squaretaper/lisbon-av-install/diagrams/kicad/esp32-led-controller-v6-kicad-bench-schematic.pdf

1 | 2 | 3 | 4 | 5 | 6 | 7 | 8
1 | 2 | 3 | 4 | 5 | 6 | 7 | 8

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
Size: A3 | Rev: v6-kicad-1 | F Date: 2026-05-20
KiCad E.D.A. 10.0.3 | Id: 1/1

# Title: ESP32 LED Controller v6 — KiCad Bench Schematic

## File: esp32-led-controller-v6.kicad_sch

## Sheet: /

## Lisbon AV installation

## ESP32 USB-powered only; common GND; AHCT125 DIP-14 top-view shown for bench wiring

1 2 C3

10µF

1

1

2

2 | J3

12V IN

1 | 2 F1

7.5A blade / off-board inline

1 | 2 R1

470Ω

1 | 2 R3

220Ω

1 | 2 R2

470Ω

A 1 | K

2 LED1

red status

1 | 2 R4

1kΩ +

+

1 -

2 C1

1000µF | / 25V
A 1 | K

2 D1

1N5822? REVIEW CURRENT

A 1 | K

2 LED2

green power-good

notch up / pin 1 upper-left DIP-14 TOP VIEW SN74AHCT125N

/OE1 1

1A 2

1Y 3 | /OE2 4

2A 5

2Y 6 | GND 7
3Y | 8
3A | 9 /OE3 | 10
4Y | | 11
4A | 12 /OE4 | 13
VCC | 14 U1

SN74AHCT125N / 74AHCT125 DIP-14

V+

1 | GND
2 | DATA 3 | J1

LED OUT 1

V+

1 | GND
2 | DATA 3 | J2

LED OUT 2

1 2 C2

0.1µF

VIN/5V = USB tap USB-C powered only ESP32 DevKit V1

GPIO25 | G25 GPIO26 | G26 GPIO27 | G27 GND | GND
VIN/5V | VIN U2
ESP32 DevKit V1 / USB only | U1_2Y U1_1Y GND +12V_IN

GND

GND | +12V_PROTECTED GND +5V_LOGIC

GND

GND +12V_PROTECTED

ESP32_GPIO27

ESP32_GPIO26

J1_DATA U1_1Y | GND
GND | +12V_PROTECTED +5V_LOGIC +5V_LOGIC

GND

# GND +12V_PROTECTED

ESP32_GPIO25 | +12V_PROTECTED +5V_LOGIC | U1_2Y | GND GND

GND

ESP32_GPIO26 | +5V_LOGIC

ESP32_GPIO27

J2_DATA

J1_DATA

# J2_DATA GND

# +5V_LOGIC +12V_IN

### ESP32_GPIO25 12 V POWER INPUT / PROTECTION

U1 unused channels: /OE3 pin10 and /OE4 pin13 → +5V_LOGIC; 3A pin9 and 4A pin12 → GND; 3Y pin8 and 4Y pin11 NC. 5 V LOGIC / STATUS

D1 current note: 1N5822 is not a free pass for multi-amp LED current. For full-current install, replace with rated protection or bypass if polarity is controlled. Bench checks before power: +12V_PROTECTED ↔ +5V_LOGIC = open/megaohms; all GND points ≈0Ω; U1 pin14 gets +5V only from ESP32 USB/VIN; never backfeed ESP32 VIN from 12 V supply.

Rails: +12V_PROTECTED powers LED V+ only. +5V_LOGIC is USB-derived from ESP32 VIN/5V only. Grounds are common. ESP32 LED Controller v6 — KiCad bench schematic

R1

470Ω

1 | 2 R2

470Ω

1 | 2
