squaretaper/lisbon-av-install/diagrams/esp32-led-controller-v6-breadboard.png

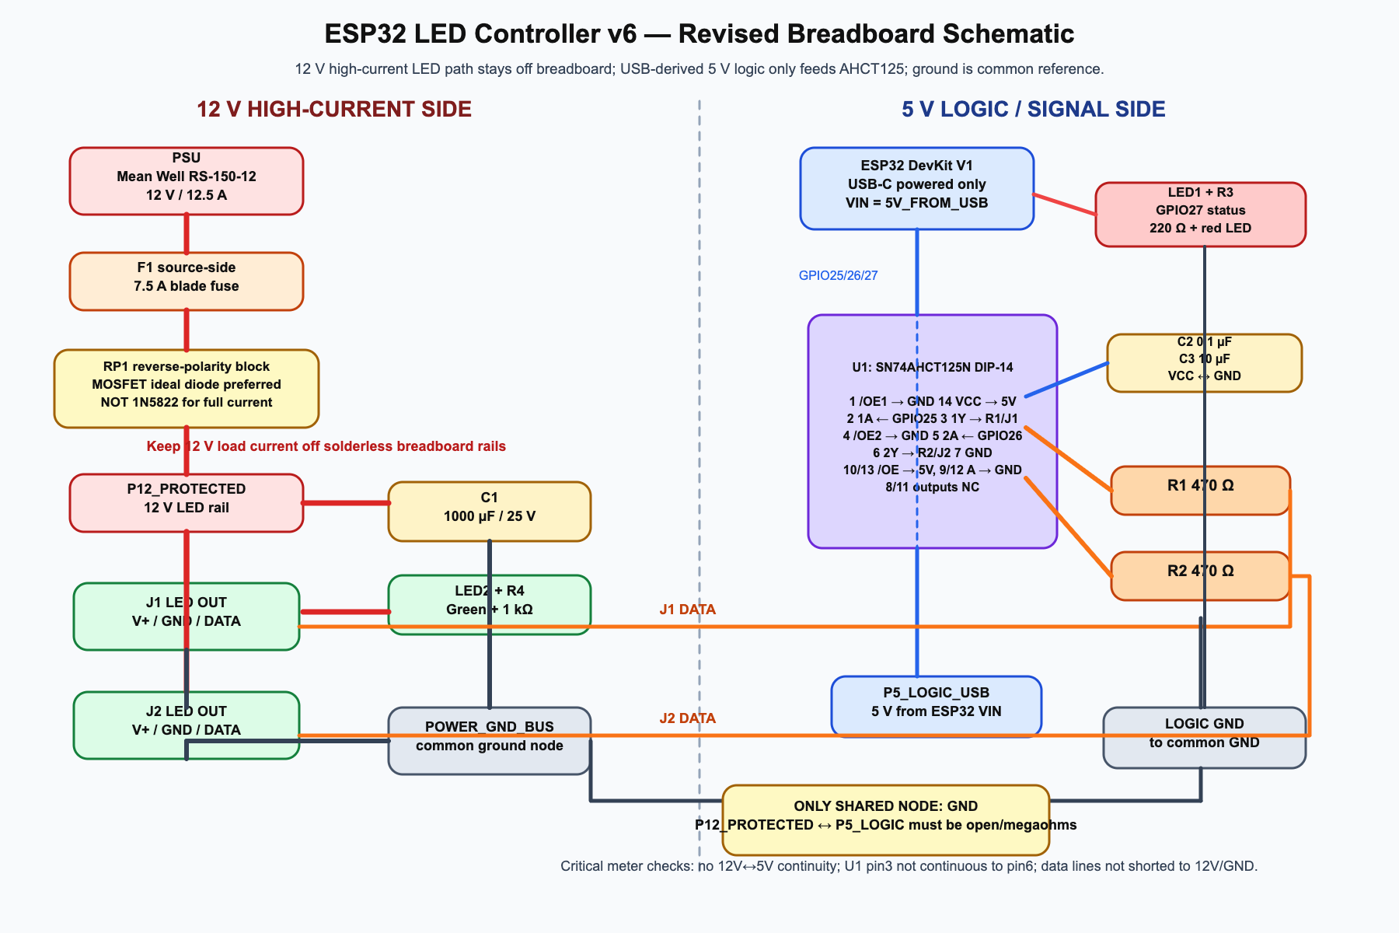
diagrams/esp32-led-controller-v6-breadboard.png
