squaretaper/lisbon-av-install/docs/esp32-breadboard/perfboard-5x7-proposed-layout.png

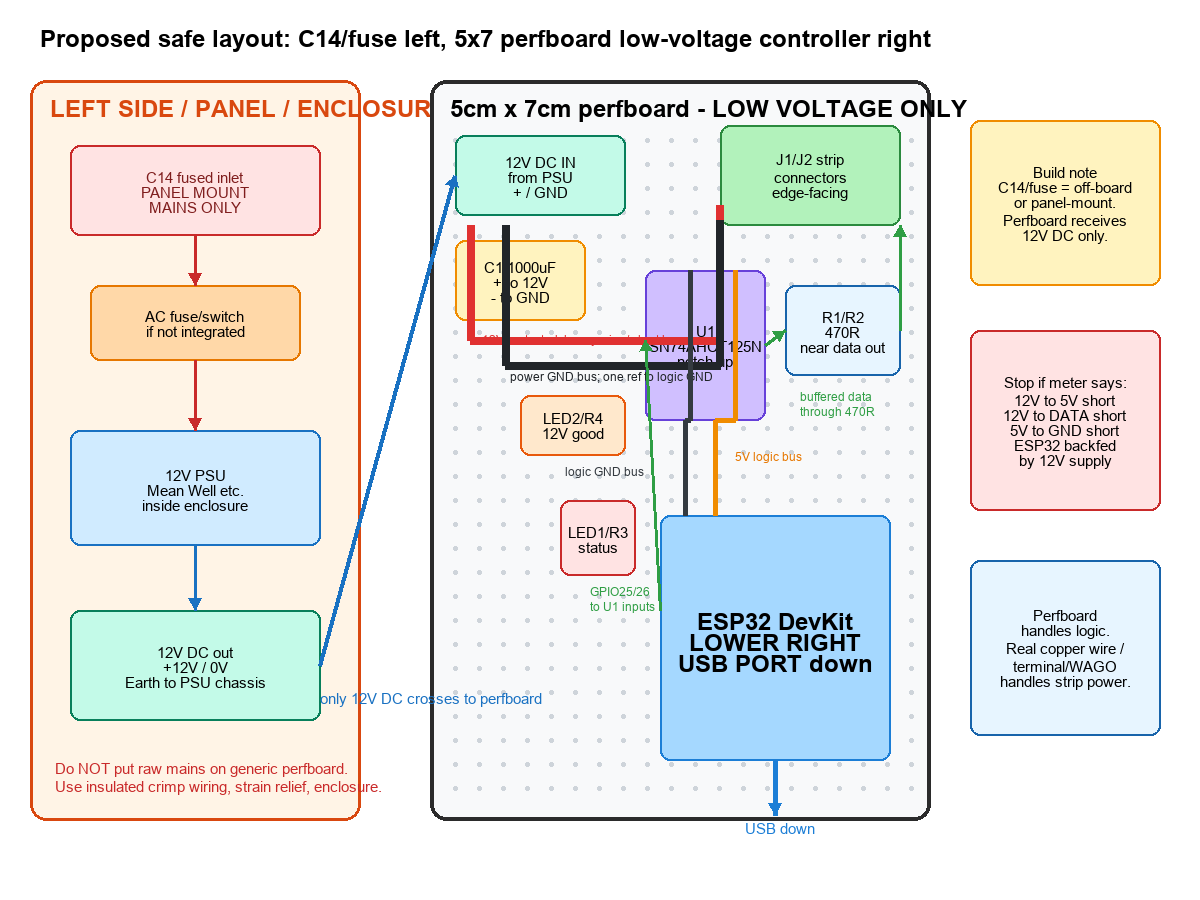
docs/esp32-breadboard/perfboard-5x7-proposed-layout.png
