squaretaper/lisbon-av-install/kicad/esp32-led-controller-v6-standard/esp32-led-controller-v6-standard.kicad_sch

## KiCad design kicad/esp32-led-controller-v6-standard/esp32-led-controller-v6-standard.kicad_sch (2026-05-28)

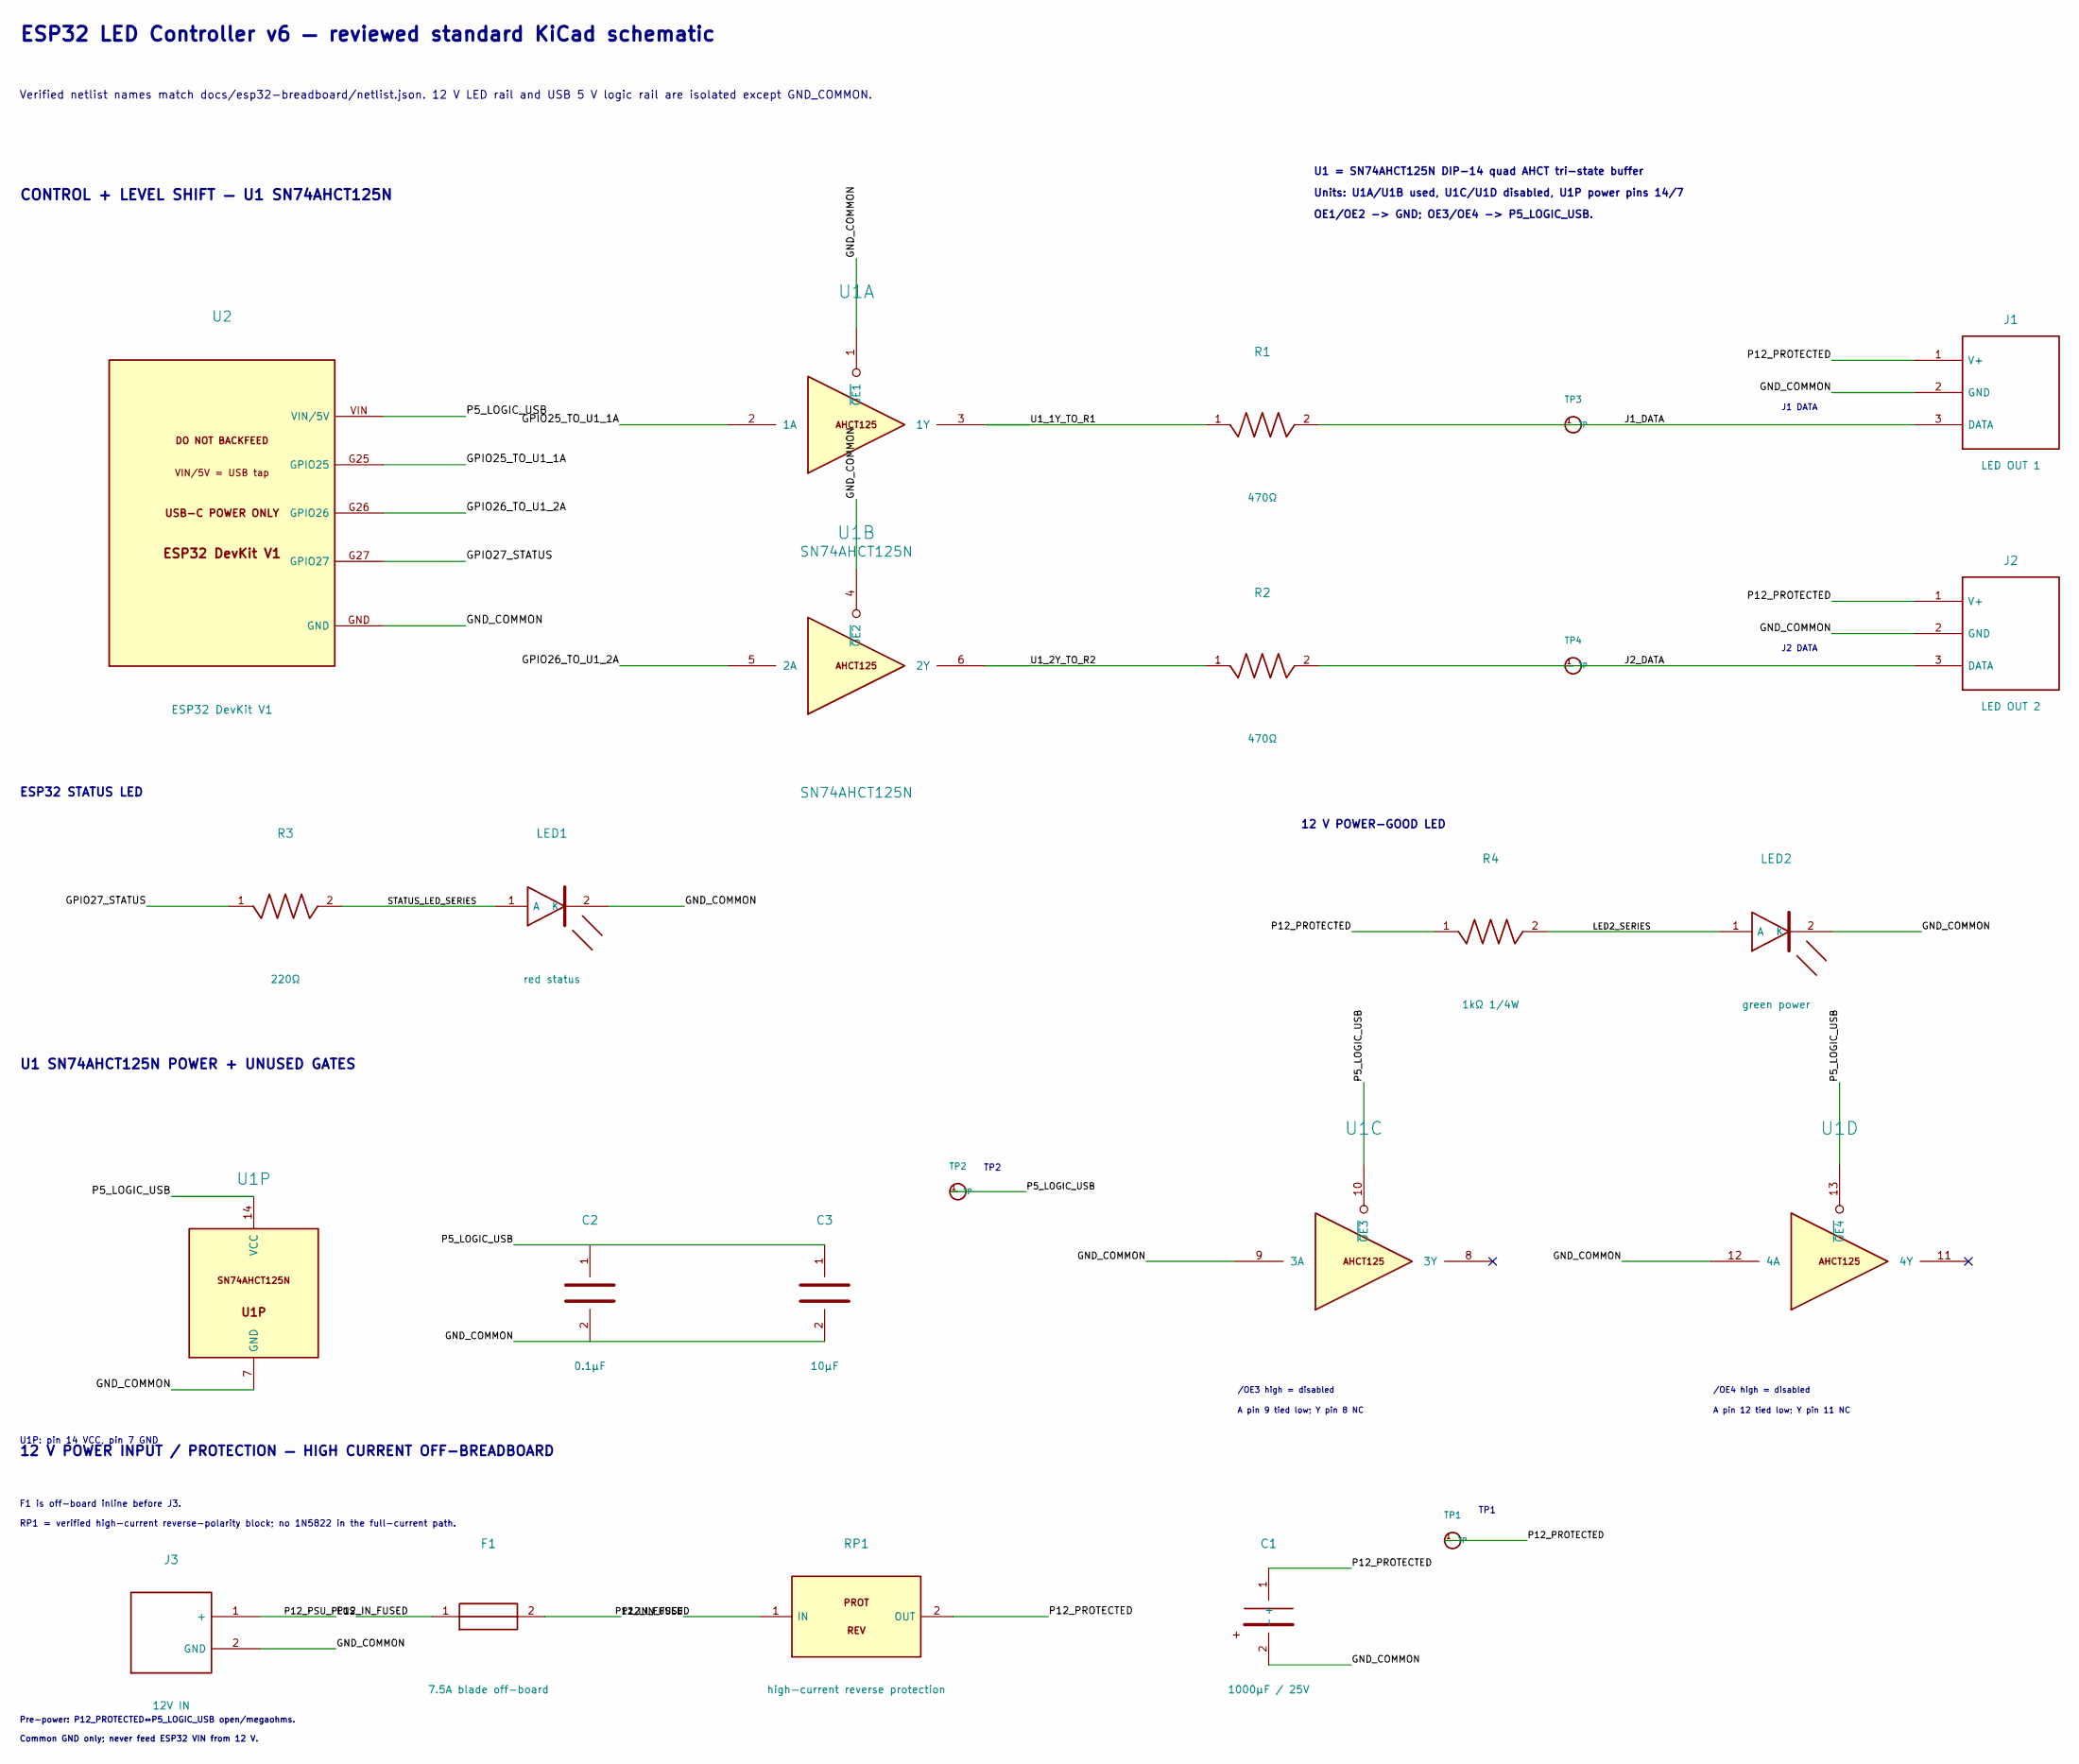
[picture p9: schematic esp32-led-controller-v6-standard.kicad_sch]

Parts:
C1: 1000µF / 25V
C2: 0.1µF
C3: 10µF
F1: 7.5A blade off-board
J1: LED OUT 1; TerminalBlock_bornier-3_P5.08mm
J2: LED OUT 2; TerminalBlock_bornier-3_P5.08mm
J3: 12V IN; TerminalBlock_bornier-2_P5.08mm
LED1: red status
LED2: green power
R1, R2: 470Ω
R3: 220Ω
R4: 1kΩ 1/4W
RP1: high-current reverse protection
TP1: P12_PROTECTED
TP2: P5_LOGIC_USB
TP3: J1_DATA
TP4: J2_DATA
U1A, U1B: SN74AHCT125N; DIP-14_W7.62mm_LongPads
U1C, U1D: SN74AHCT125N unused
U1P: SN74AHCT125N power; DIP-14_W7.62mm_LongPads
U2: ESP32 DevKit V1

Connections:
GND_COMMON: C1.2 (-), C2.2, C3.2, J1.2 (GND), J2.2 (GND), J3.2 (GND), LED1.2 (K), LED2.2 (K), U1A.1 (~OE1), U1B.4 (~OE2), U1C.9 (3A), U1D.12 (4A), U1P.7 (GND), U2.GND
GPIO25_TO_U1_1A: U1A.2 (1A), U2.G25 (GPIO25)
GPIO26_TO_U1_2A: U1B.5 (2A), U2.G26 (GPIO26)
GPIO27_STATUS: R3.1, U2.G27 (GPIO27)
J1_DATA: J1.3 (DATA), R1.2, TP3.1
J2_DATA: J2.3 (DATA), R2.2, TP4.1
LED2_SERIES: LED2.1 (A), R4.2
P5_LOGIC_USB: C2.1, C3.1, TP2.1, U1C.10 (~OE3), U1D.13 (~OE4), U1P.14 (VCC), U2.VIN (VIN/5V)
P12_IN_FUSED: F1.2, J3.1 (+), RP1.1 (IN)
P12_PROTECTED: C1.1 (+), J1.1 (V+), J2.1 (V+), R4.1, RP1.2 (OUT), TP1.1
P12_PSU_PLUS: F1.1
STATUS_LED_SERIES: LED1.1 (A), R3.2
U1_1Y_TO_R1: R1.1, U1A.3 (1Y)
U1_2Y_TO_R2: R2.1, U1B.6 (2Y)

Notes on the sheet:
ESP32 LED Controller v6 — reviewed standard KiCad schematic
Verified netlist names match docs/esp32-breadboard/netlist.json. 12 V LED rail and USB 5 V logic rail are isolated except GND_COMMON.
CONTROL + LEVEL SHIFT — U1 SN74AHCT125N
U1 = SN74AHCT125N DIP-14 quad AHCT tri-state buffer
Units: U1A/U1B used, U1C/U1D disabled, U1P power pins 14/7
OE1/OE2 -> GND; OE3/OE4 -> P5_LOGIC_USB.
J1 DATA
J2 DATA
ESP32 STATUS LED
U1 SN74AHCT125N POWER + UNUSED GATES
U1P: pin 14 VCC, pin 7 GND
TP2
/OE3 high = disabled
A pin 9 tied low; Y pin 8 NC
/OE4 high = disabled
A pin 12 tied low; Y pin 11 NC
12 V POWER INPUT / PROTECTION — HIGH CURRENT OFF-BREADBOARD
F1 is off-board inline before J3.
RP1 = verified high-current reverse-polarity block; no 1N5822 in the full-current path.
TP1
12 V POWER-GOOD LED
Pre-power: P12_PROTECTED↔P5_LOGIC_USB open/megaohms.
Common GND only; never feed ESP32 VIN from 12 V.
