squaretaper/lisbon-av-install/kicad/esp32-led-controller-v6/esp32-led-controller-v6.kicad_sch

## KiCad design kicad/esp32-led-controller-v6/esp32-led-controller-v6.kicad_sch (2026-05-28)

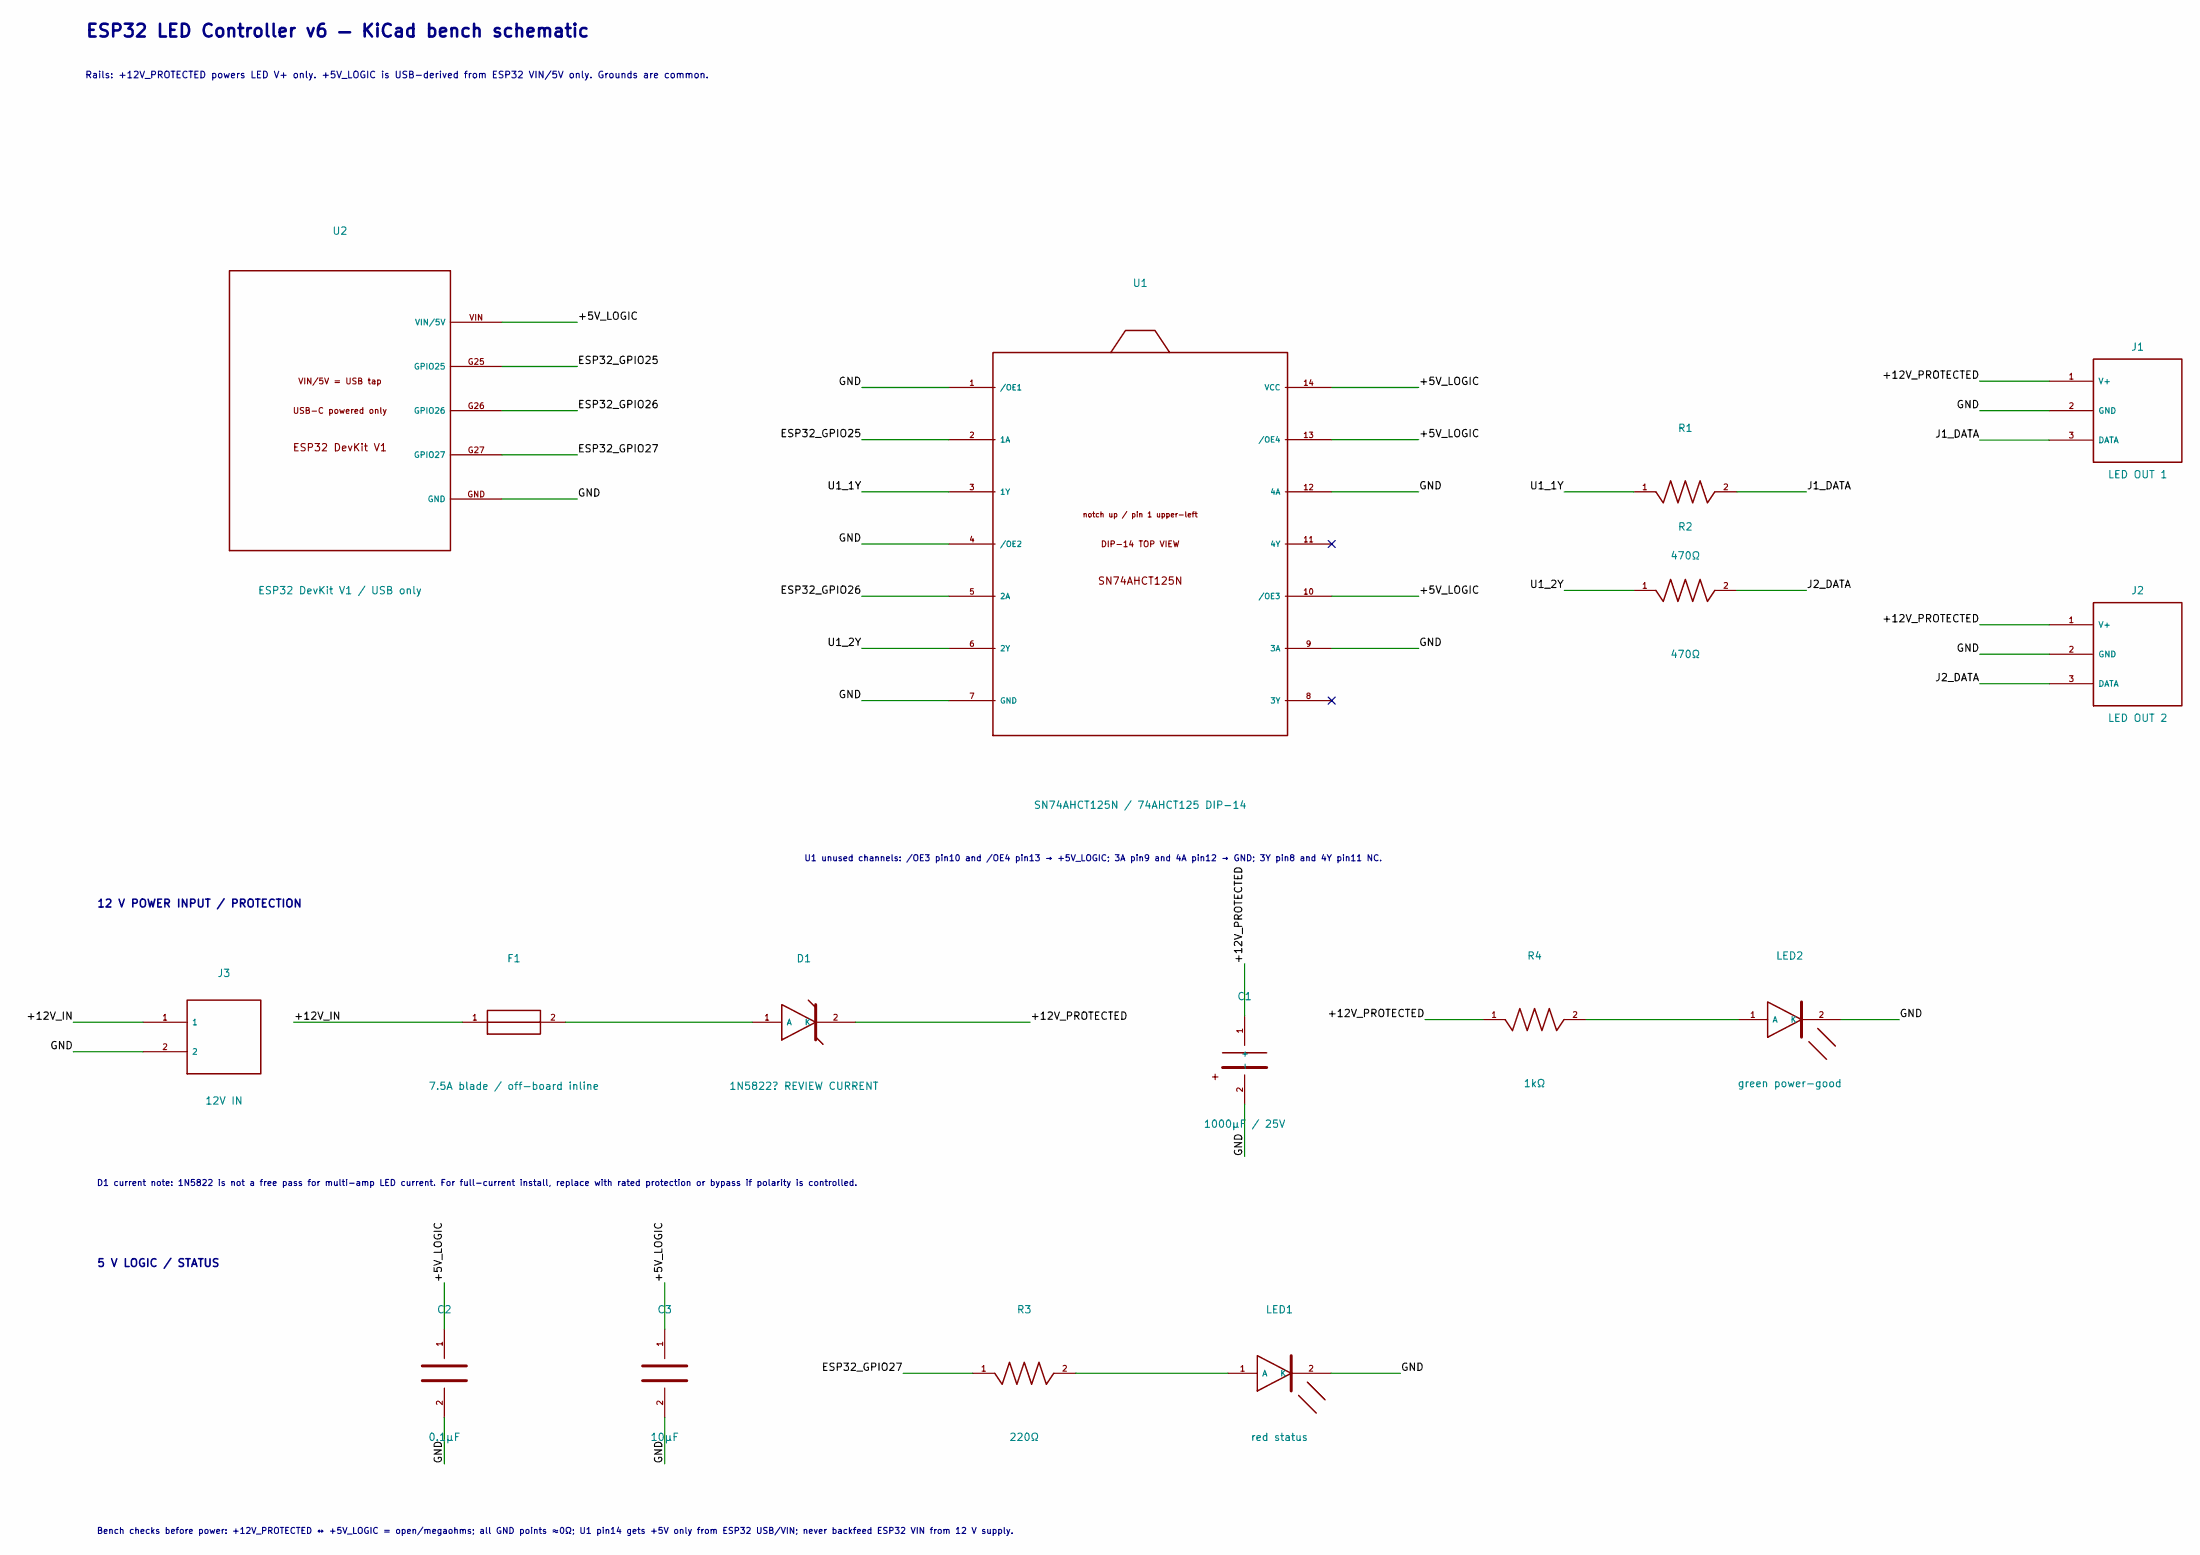
[picture p10: schematic esp32-led-controller-v6.kicad_sch]

Parts:
C1: 1000µF / 25V; CP_Radial_D10.0mm_P5.00mm
C2: 0.1µF
C3: 10µF
D1: 1N5822? REVIEW CURRENT; D_DO-201AD_P15.24mm_Horizontal
F1: 7.5A blade / off-board inline
J1: LED OUT 1; TerminalBlock_bornier-3_P5.08mm
J2: LED OUT 2; TerminalBlock_bornier-3_P5.08mm
J3: 12V IN; TerminalBlock_bornier-2_P5.08mm
LED1: red status
LED2: green power-good
R1, R2: 470Ω; R_Axial_DIN0207_L6.3mm_D2.5mm_P10.16mm_Horizontal
R3: 220Ω
R4: 1kΩ
U1: SN74AHCT125N / 74AHCT125 DIP-14; DIP-14_W7.62mm_LongPads
U2: ESP32 DevKit V1 / USB only

Connections:
+5V_LOGIC: C2.1, C3.1, U1.10 (/OE3), U1.13 (/OE4), U1.14 (VCC), U2.VIN (VIN/5V)
+12V_IN: F1.1, J3.1
+12V_PROTECTED: C1.1 (+), D1.2 (K), J1.1 (V+), J2.1 (V+), R4.1
ESP32_GPIO25: U1.2 (1A), U2.G25 (GPIO25)
ESP32_GPIO26: U1.5 (2A), U2.G26 (GPIO26)
ESP32_GPIO27: R3.1, U2.G27 (GPIO27)
GND: C1.2 (-), C2.2, C3.2, J1.2 (GND), J2.2 (GND), J3.2, LED1.2 (K), LED2.2 (K), U1.1 (/OE1), U1.4 (/OE2), U1.7 (GND), U1.9 (3A), U1.12 (4A), U2.GND
J1_DATA: J1.3 (DATA), R1.2
J2_DATA: J2.3 (DATA), R2.2
unnamed: D1.1 (A), F1.2
unnamed: LED1.1 (A), R3.2
unnamed: LED2.1 (A), R4.2
U1_1Y: R1.1, U1.3 (1Y)
U1_2Y: R2.1, U1.6 (2Y)

Notes on the sheet:
ESP32 LED Controller v6 — KiCad bench schematic
Rails: +12V_PROTECTED powers LED V+ only. +5V_LOGIC is USB-derived from ESP32 VIN/5V only. Grounds are common.
U1 unused channels: /OE3 pin10 and /OE4 pin13 → +5V_LOGIC; 3A pin9 and 4A pin12 → GND; 3Y pin8 and 4Y pin11 NC.
12 V POWER INPUT / PROTECTION
D1 current note: 1N5822 is not a free pass for multi-amp LED current. For full-current install, replace with rated protection or bypass if polarity is controlled.
5 V LOGIC / STATUS
Bench checks before power: +12V_PROTECTED ↔ +5V_LOGIC = open/megaohms; all GND points ≈0Ω; U1 pin14 gets +5V only from ESP32 USB/VIN; never backfeed ESP32 VIN from 12 V supply.
